TADilhara/3YP-ME325-/Field_Observations_01/Images/IMG_1.jpg

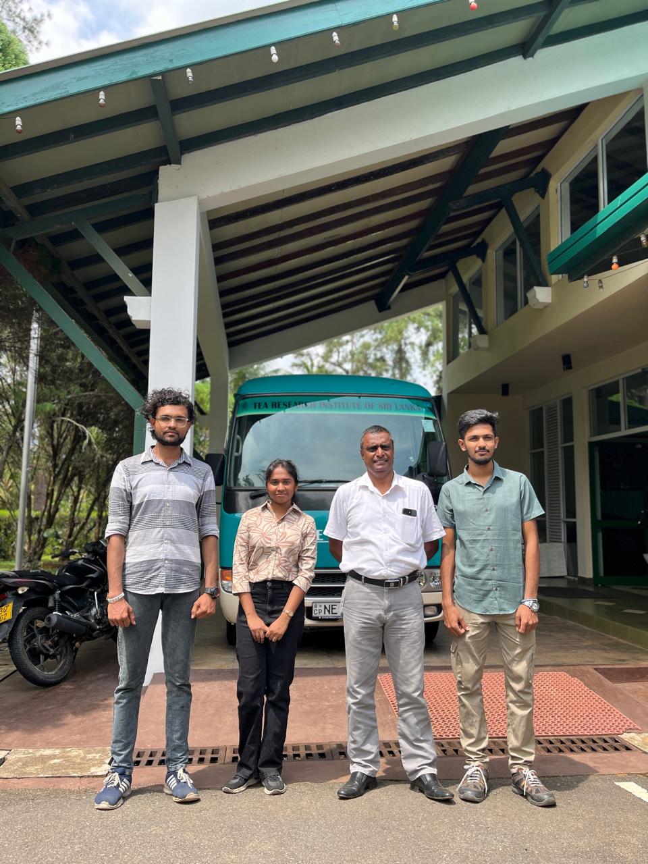
Field_Observations_01/Images/IMG_1.jpg
