TADilhara/3YP-ME325-/Field_Observations_01/Images/IMG_2.jpg

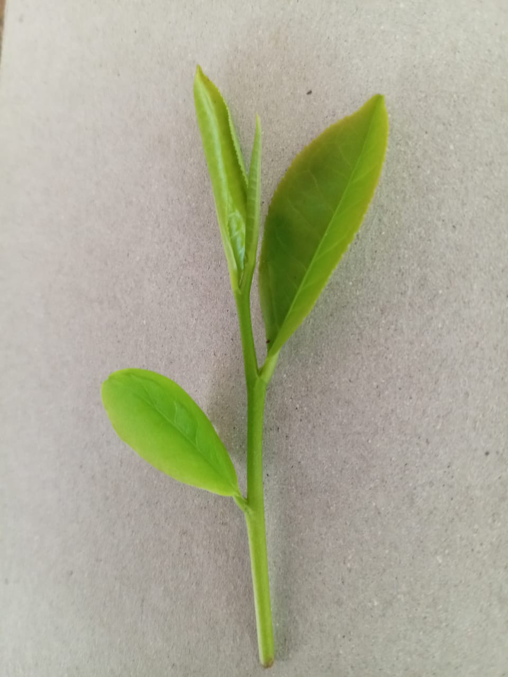
Field_Observations_01/Images/IMG_2.jpg
