TADilhara/3YP-ME325-/Field_Observations_01/Images/IMG_4.jpeg

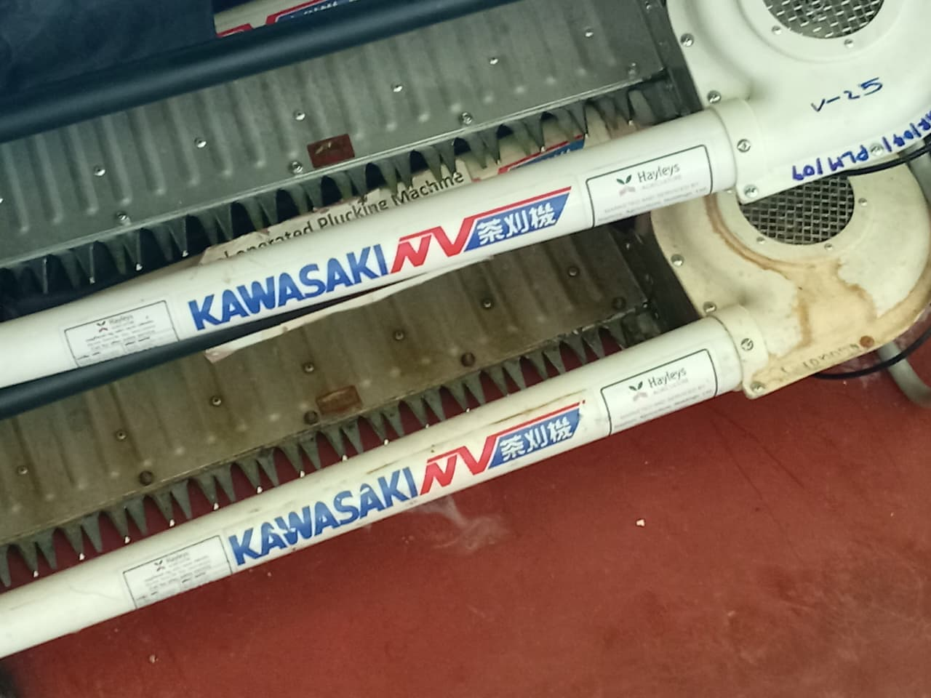
Field_Observations_01/Images/IMG_4.jpeg
