TADilhara/3YP-ME325-/Field_Observations_01/Images/IMG_7.jpeg

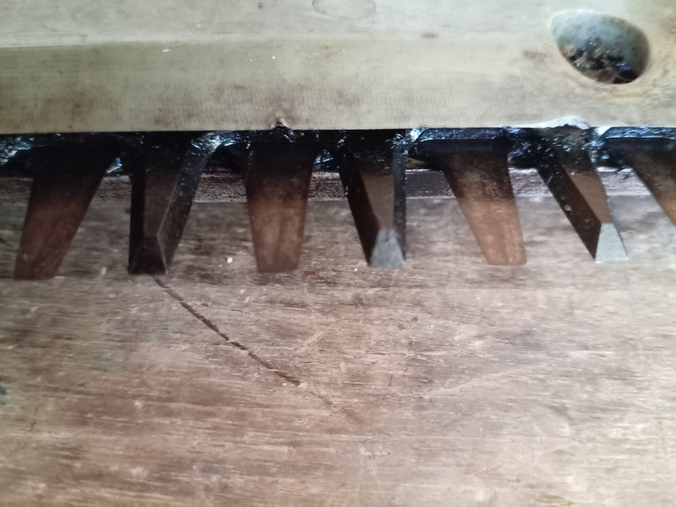
Field_Observations_01/Images/IMG_7.jpeg
