TADilhara/3YP-ME325-/Field_Observations_02/Images/IMG_1.jpeg

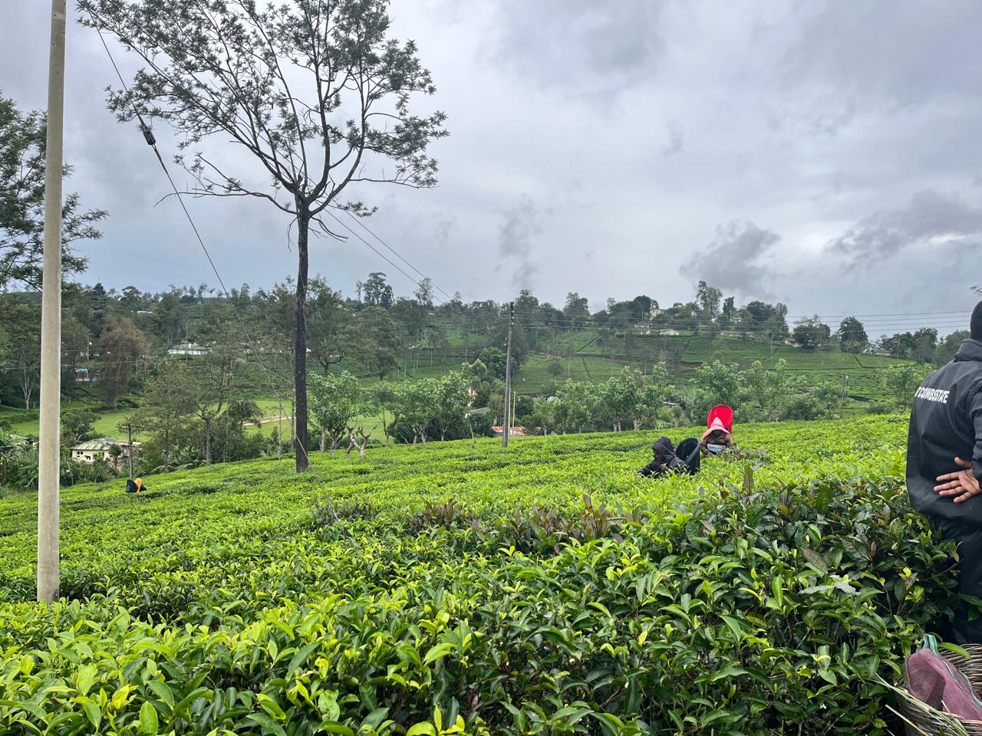
Field_Observations_02/Images/IMG_1.jpeg
