TADilhara/3YP-ME325-/Field_Observations_02/Images/IMG_5.jpeg

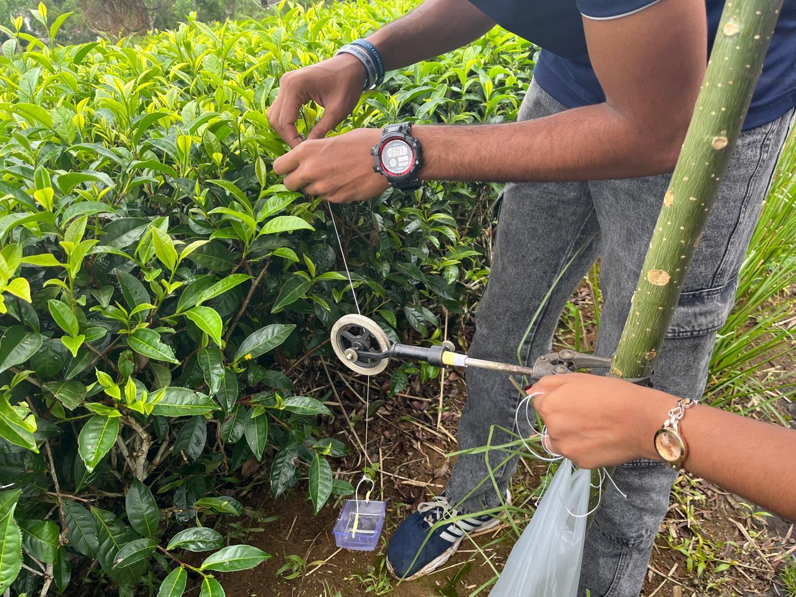
Field_Observations_02/Images/IMG_5.jpeg
