TADilhara/3YP-ME325-/Field_Observations_02/Images/IMG_6.jpeg

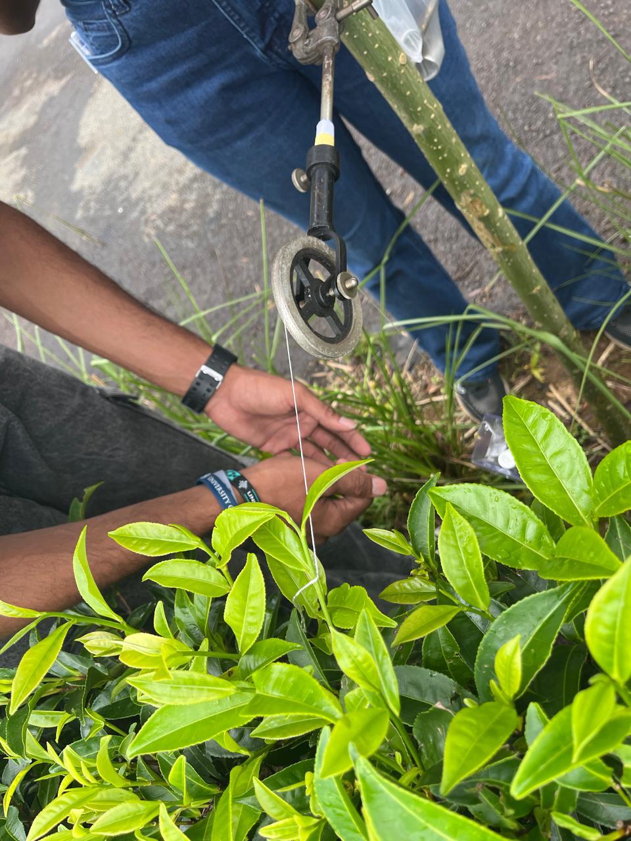
Field_Observations_02/Images/IMG_6.jpeg
