TADilhara/3YP-ME325-/Field_Observations_02/Images/IMG_7.jpeg

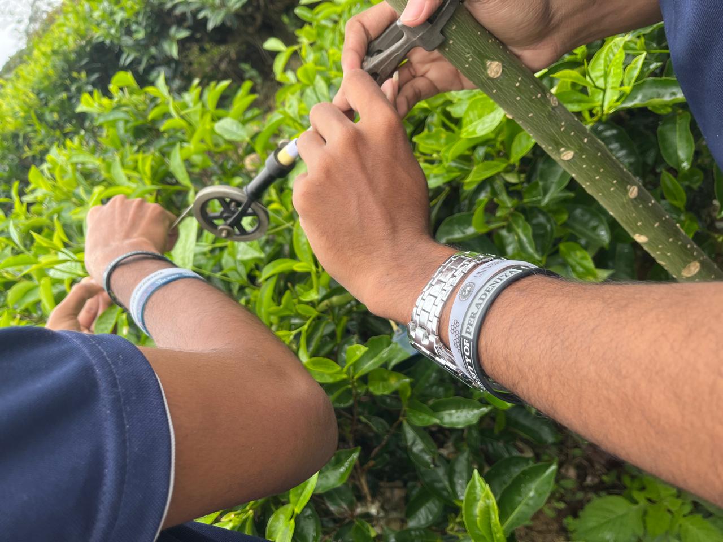
Field_Observations_02/Images/IMG_7.jpeg
