TADilhara/3YP-ME325-/Field_Observations_02/Tea_Bending_Force_Analysis/Tea_Shoot_Force_Distribution_Chart.png

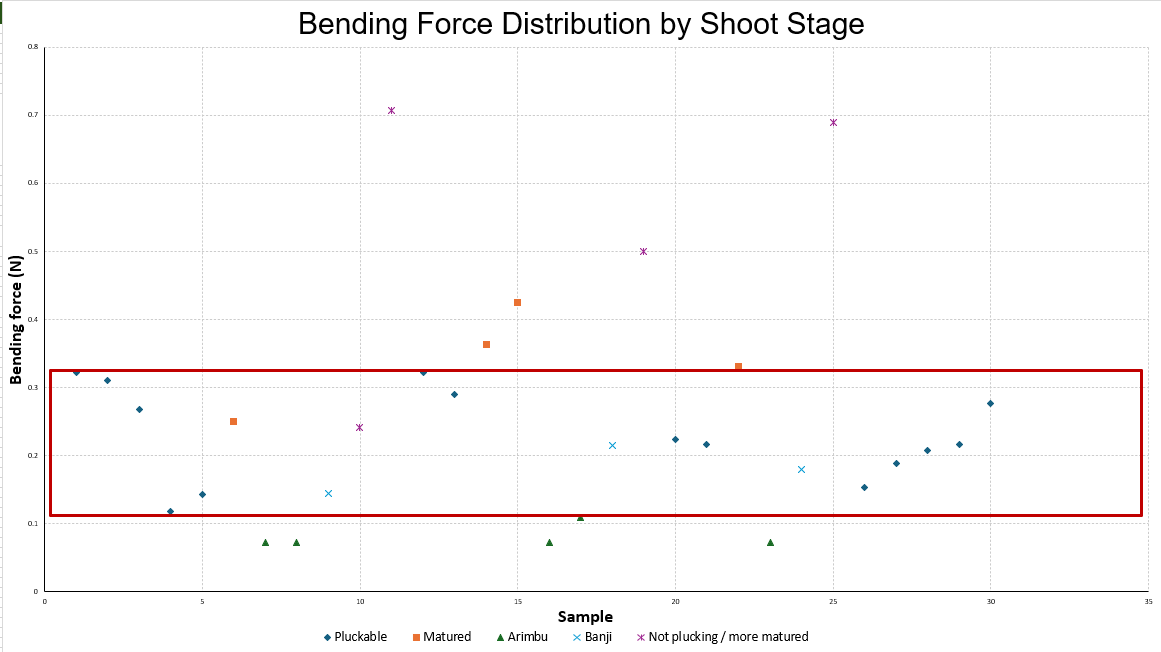
Field_Observations_02/Tea_Bending_Force_Analysis/Tea_Shoot_Force_Distribution_Chart.png
