TADilhara/3YP-ME325-/Field_Observations_03/images/IMG_5.jpeg

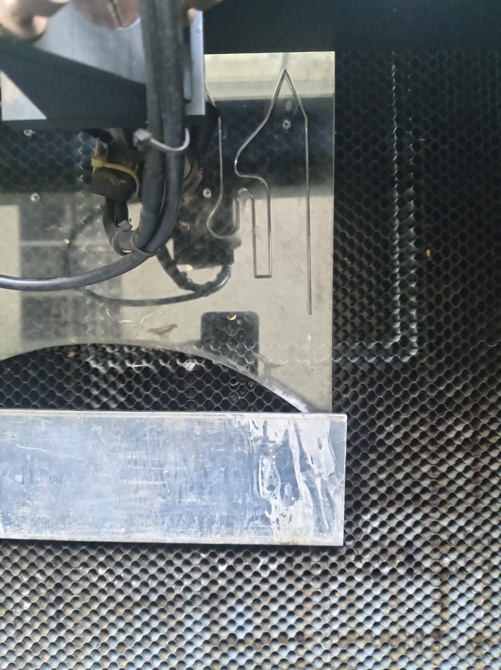
Field_Observations_03/images/IMG_5.jpeg
